ProjetoPetAzul/PROJETOPET_ENTREGADOR/media/images/openscad/photo_5003700921082514616_w.jpg

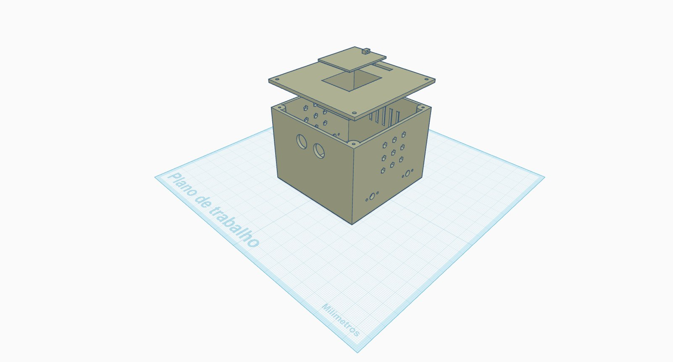
media/images/openscad/photo_5003700921082514616_w.jpg
