ProjetoPetAzul/PROJETOPET_ENTREGADOR/media/images/openscad/photo_5022031515084327990_y.jpg

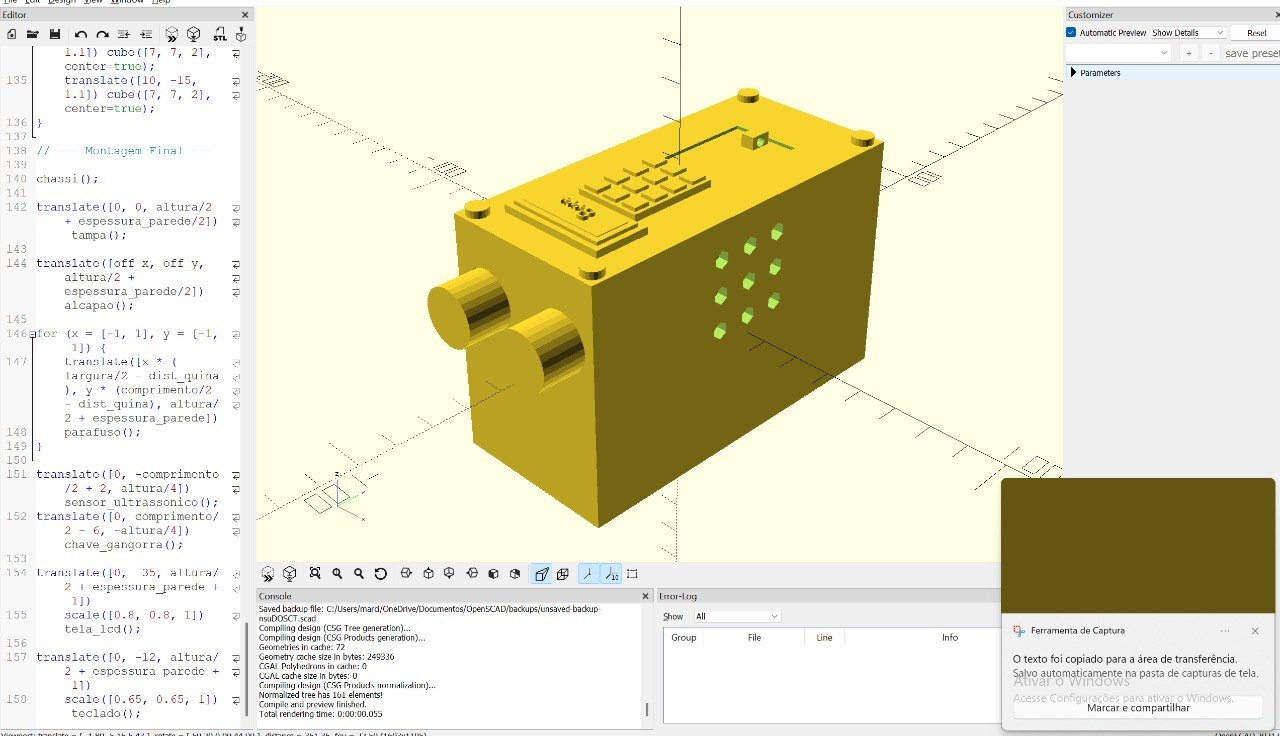
media/images/openscad/photo_5022031515084327990_y.jpg
