ProjetoPetAzul/PROJETOPET_ENTREGADOR/media/images/prototipo/photo_5022031515084327991_y.jpg

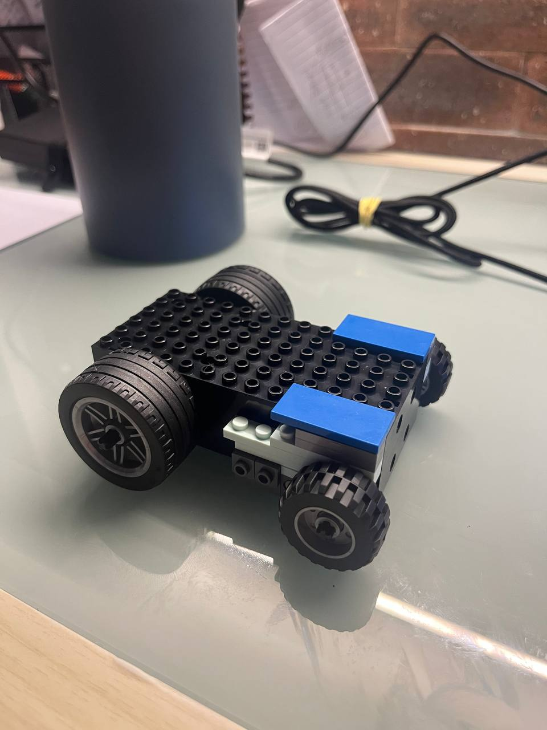
media/images/prototipo/photo_5022031515084327991_y.jpg
