ProjetoPetAzul/PROJETOPET_ENTREGADOR/media/images/tinkercad/Captura de tela 2026-09-27 202006.jpg

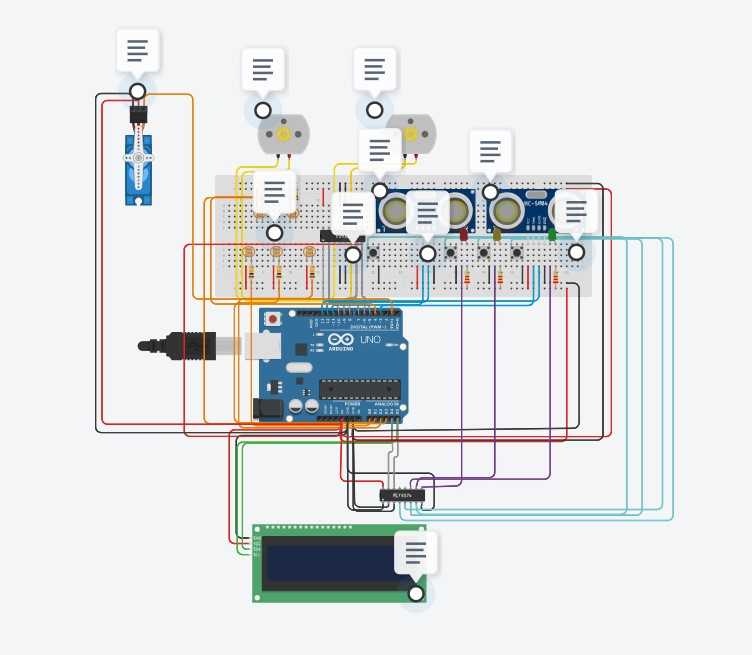
media/images/tinkercad/Captura de tela 2026-09-27 202006.jpg
