ProjetoPetAzul/PROJETOPET_ENTREGADOR/media/images/tinkercad/Captura de tela 2026-09-27 202048.jpg

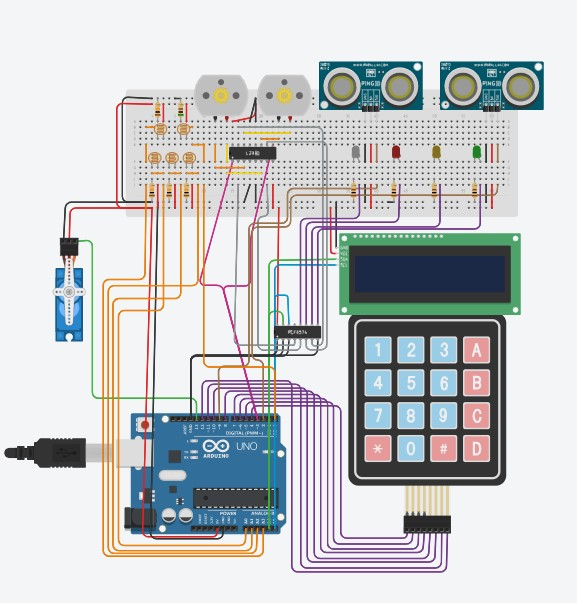
media/images/tinkercad/Captura de tela 2026-09-27 202048.jpg
