ProjetoPetAzul/PROJETOPET_ENTREGADOR/media/images/webots/Captura de tela 2026-09-27 200331.png

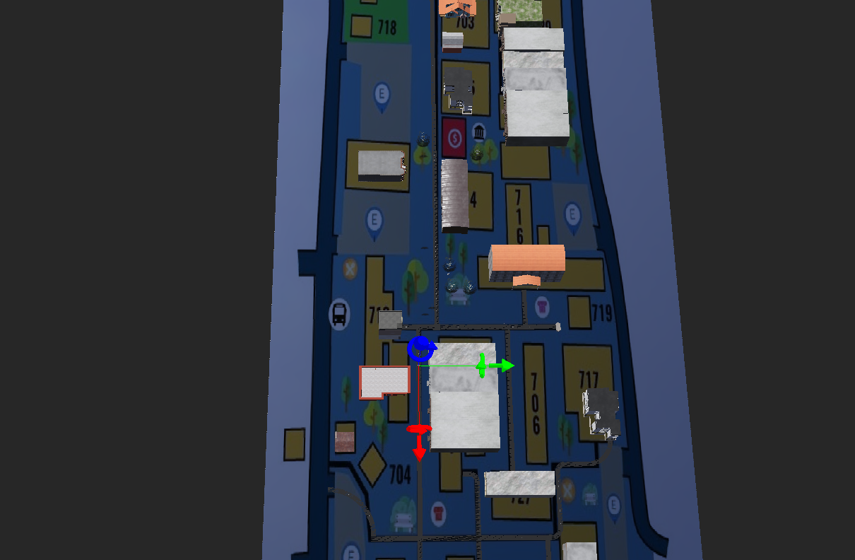
media/images/webots/Captura de tela 2026-09-27 200331.png
