ProjetoPetAzul/PROJETOPET_ENTREGADOR/media/images/webots/photo_5030813907160862119_y.jpg

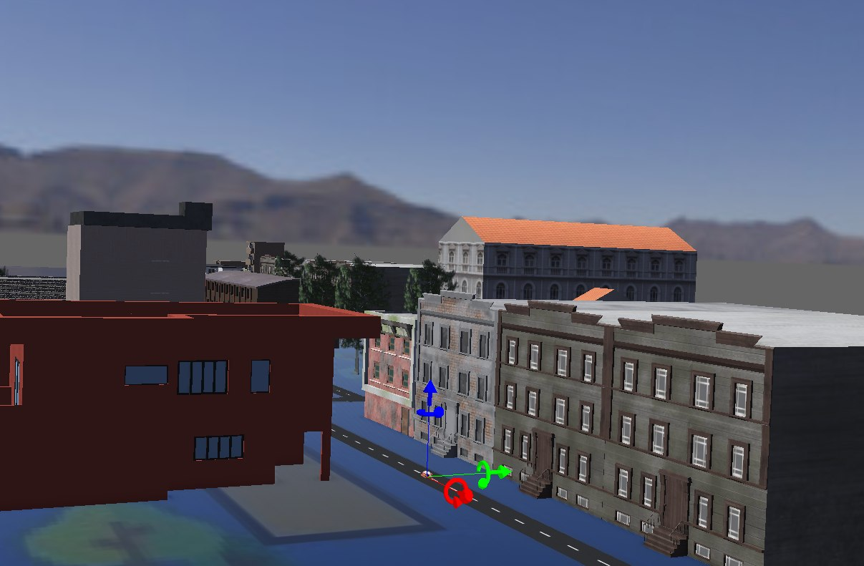
media/images/webots/photo_5030813907160862119_y.jpg
