ProjetoPetAzul/PROJETOPET_ENTREGADOR/webots/worlds/.criar.jpg

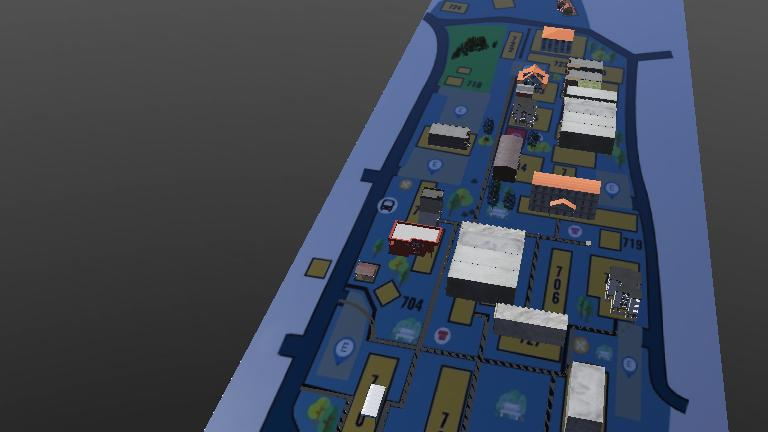
webots/worlds/.criar.jpg
