ProjetoPetAzul/PROJETOPET_ENTREGADOR/webots/worlds/textures/centro_de_tecnologia.jpg

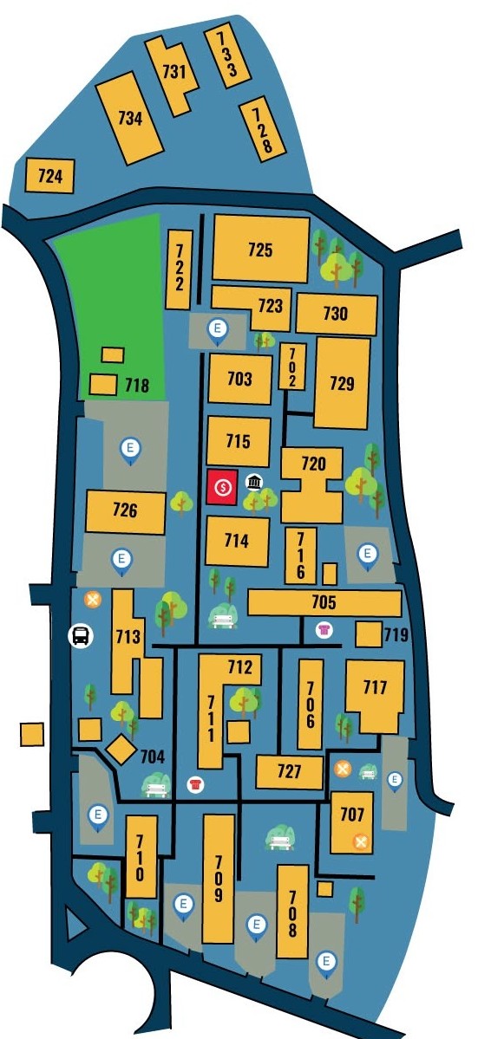
webots/worlds/textures/centro_de_tecnologia.jpg
